RepRapLtd/WiControl/ESP-8266/UsedRepos/ESP8266 /TOP VIEW.jpg

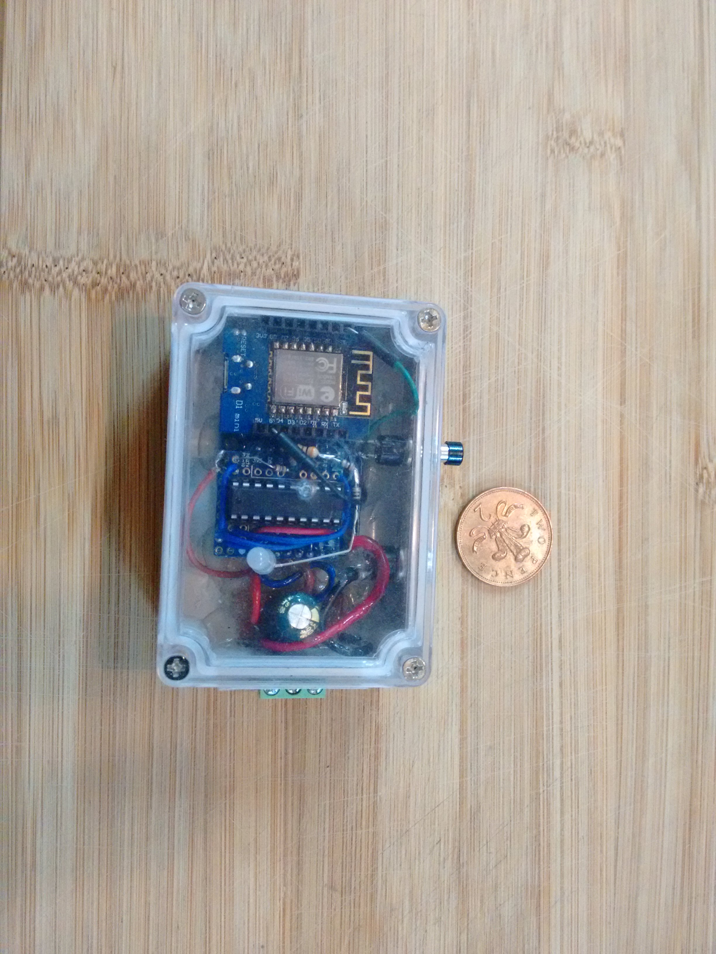
ESP-8266/UsedRepos/ESP8266 /TOP VIEW.jpg
