RepRapLtd/WiControl/ESP-8266/Electronics/KiCAD/SB - wifiboard-v2.png

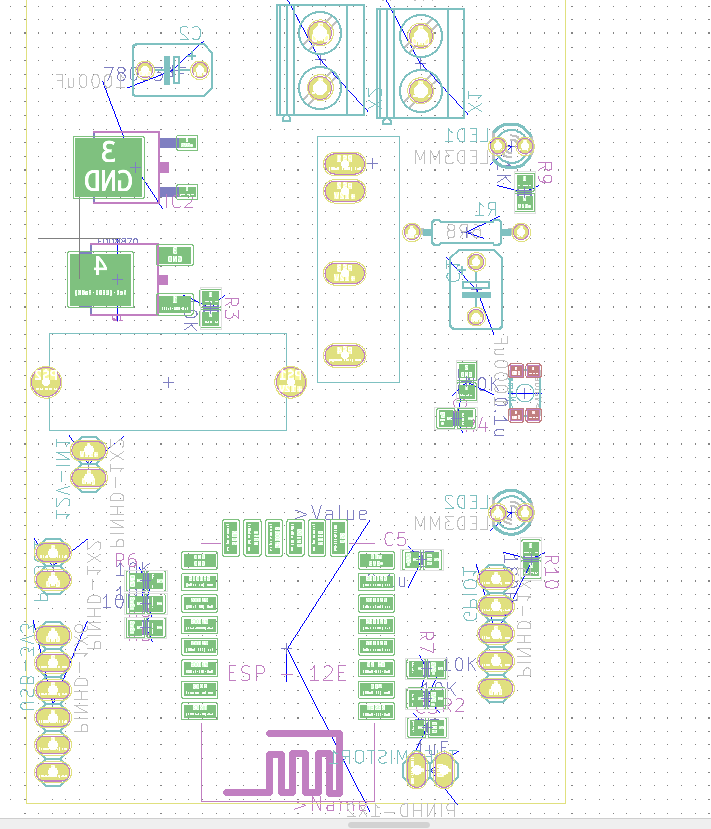
ESP-8266/Electronics/KiCAD/SB - wifiboard-v2.png
