RepRapLtd/WiControl/ESP-8266/UsedRepos/ESP8266 /OUTPUTS.jpg

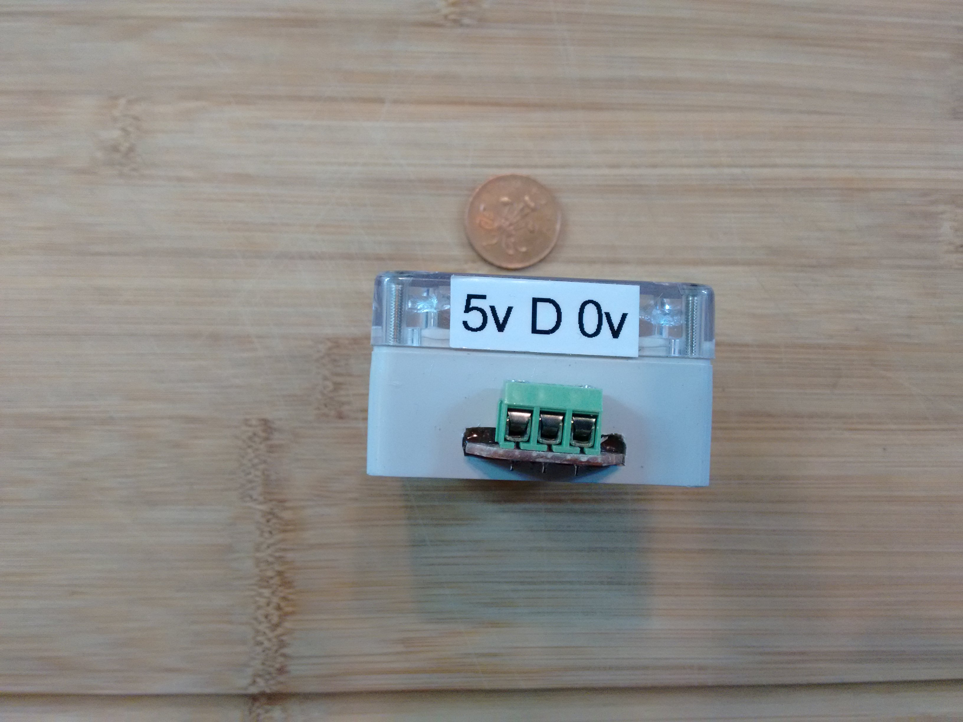
ESP-8266/UsedRepos/ESP8266 /OUTPUTS.jpg
