RepRapLtd/WiControl/ESP-8266/UsedRepos/ESP8266 /RESET BUTTON AND PSU PLUG.jpg

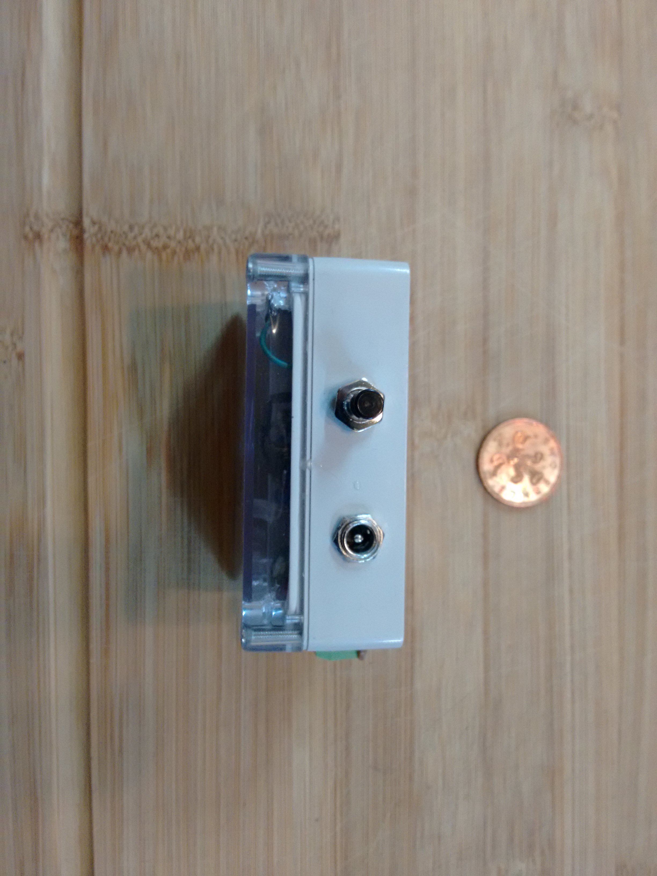
ESP-8266/UsedRepos/ESP8266 /RESET BUTTON AND PSU PLUG.jpg
