RepRapLtd/WiControl/ESP-8266/UsedRepos/ESP8266 /Wemos D1 ws2812b.jpg

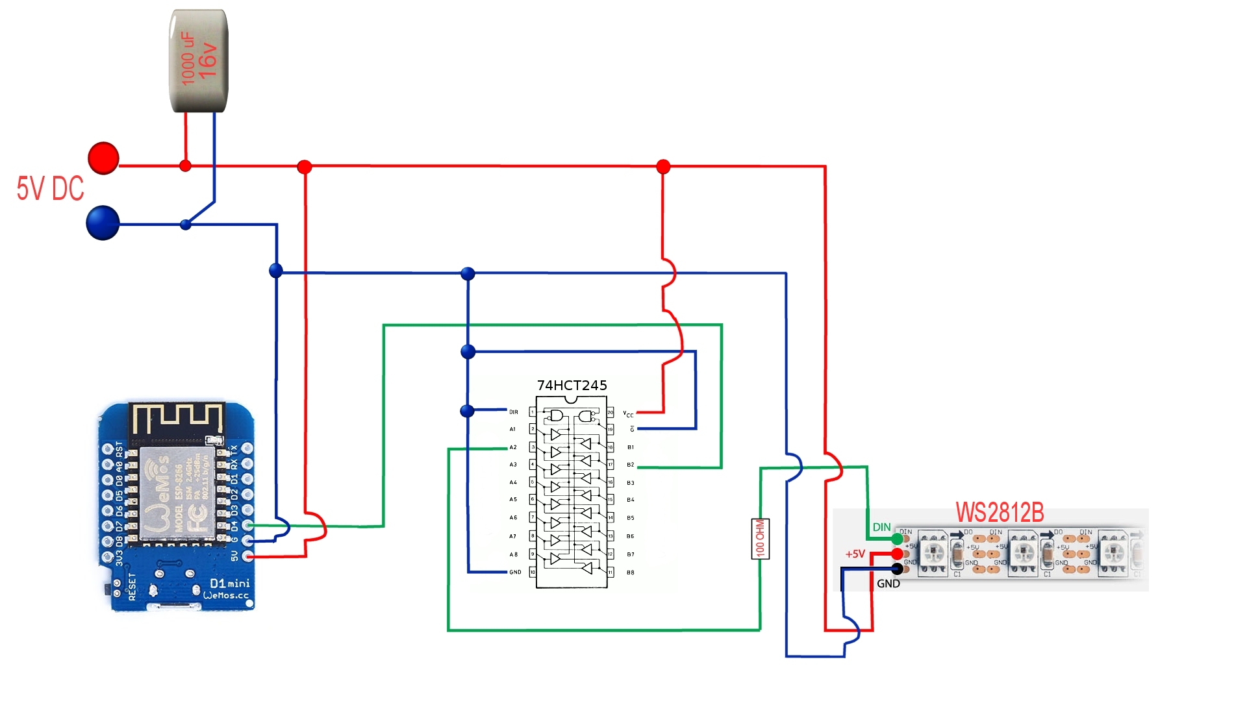
ESP-8266/UsedRepos/ESP8266 /Wemos D1 ws2812b.jpg
