RepRapLtd/WiControl/Reprogrammed-switches/swa1.jpg

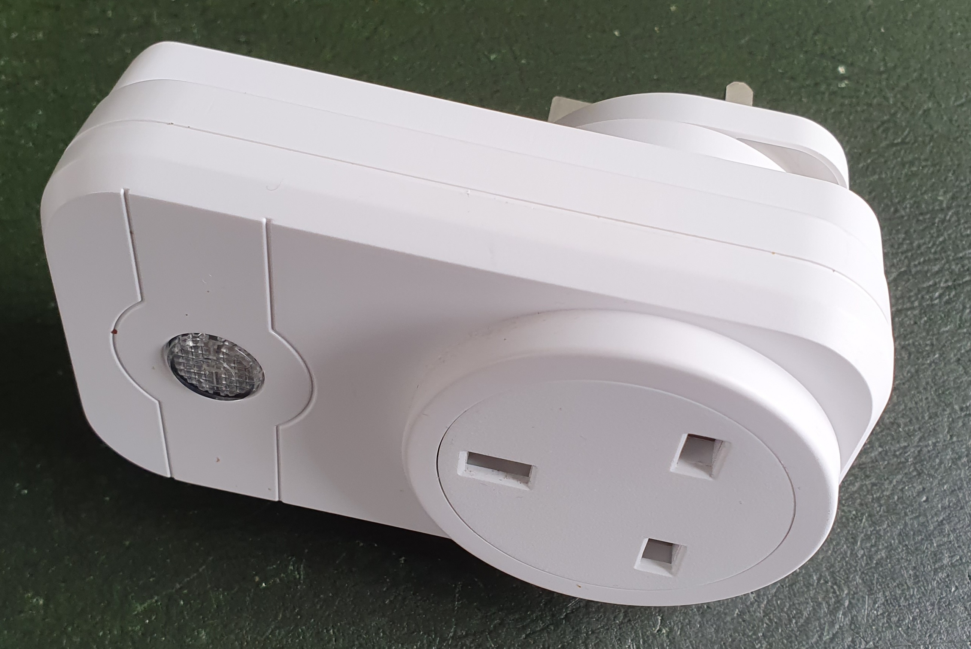
Reprogrammed-switches/swa1.jpg
