RepRapLtd/WiControl/ESP-8266/Mechanics/STLs/Wifi Patress Box/Wifi Patress-Cut014.stl

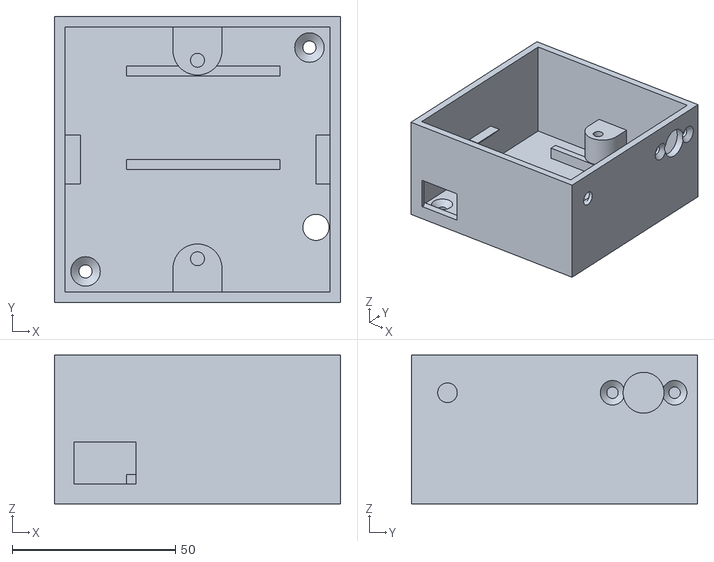
[picture p23: CAD file, 2021-06-18]
ESP-8266/Mechanics/STLs/Wifi Patress Box/Wifi Patress-Cut014.stl
87.5 x 87.5 x 45.5
