RepRapLtd/WiControl/PanStamp/Mechanical/long-lid.stl

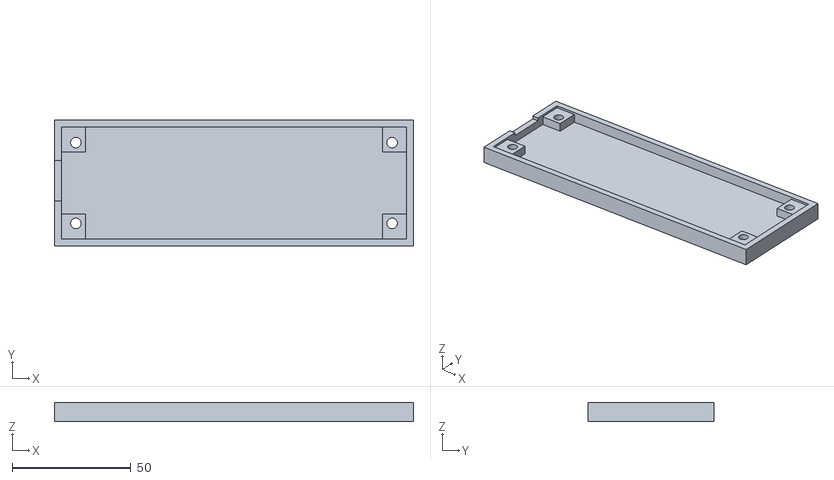
[picture p24: CAD file, 2014-07-27]
PanStamp/Mechanical/long-lid.stl
151.0 x 53.0 x 8.00
