RepRapLtd/WiControl/ESP-8266/Mechanics/Disc-STLs/walls.stl

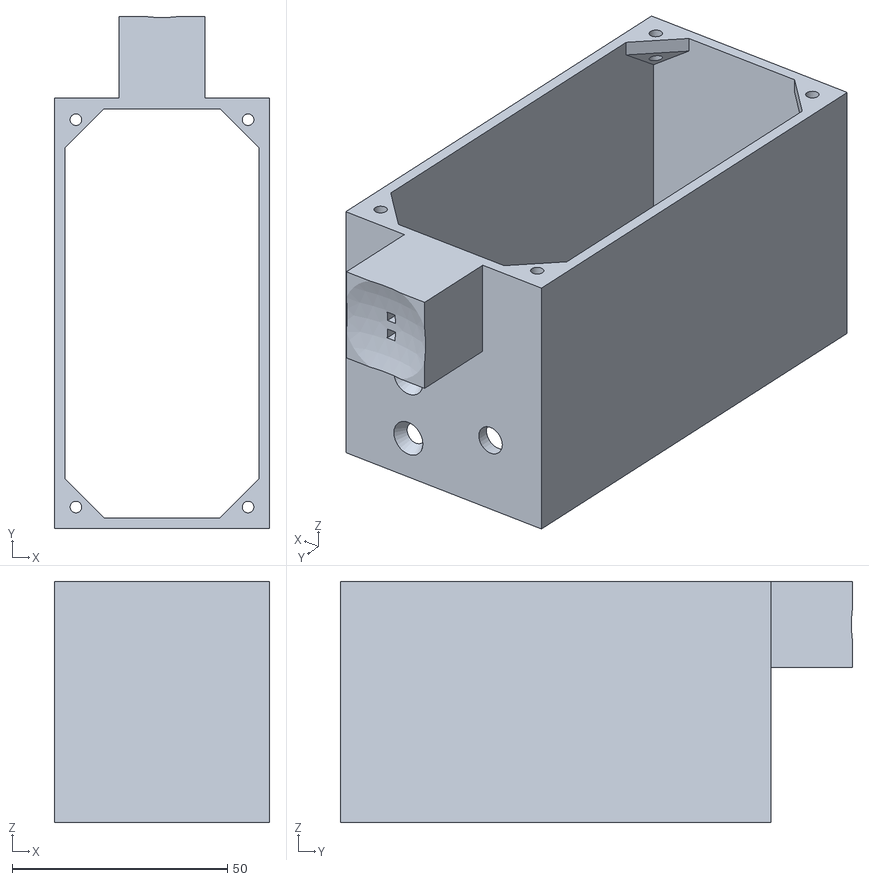
[picture p25: CAD file, 2018-09-07]
ESP-8266/Mechanics/Disc-STLs/walls.stl
50.0 x 119.0 x 56.0
