RepRapLtd/WiControl/ESP-8266/Mechanics/STLs/Bump-STLs/separator.stl

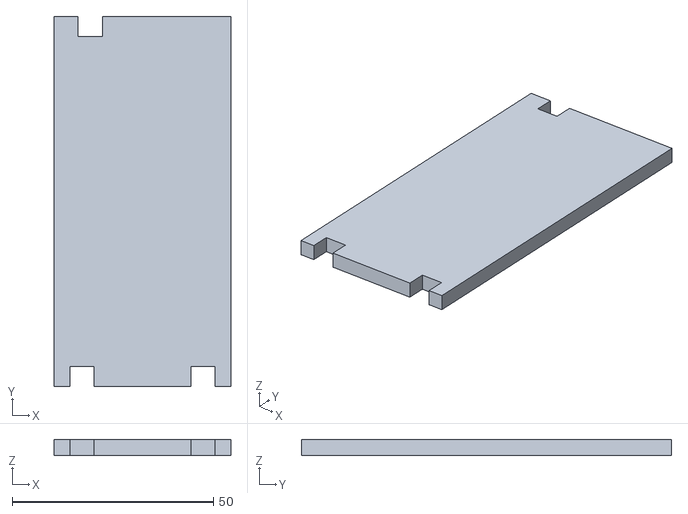
[picture p26: CAD file, 2018-09-18]
ESP-8266/Mechanics/STLs/Bump-STLs/separator.stl
44.0 x 92.0 x 4.00
