RepRapLtd/WiControl/ESP-8266/Mechanics/STLs/temp-wall-mount.stl

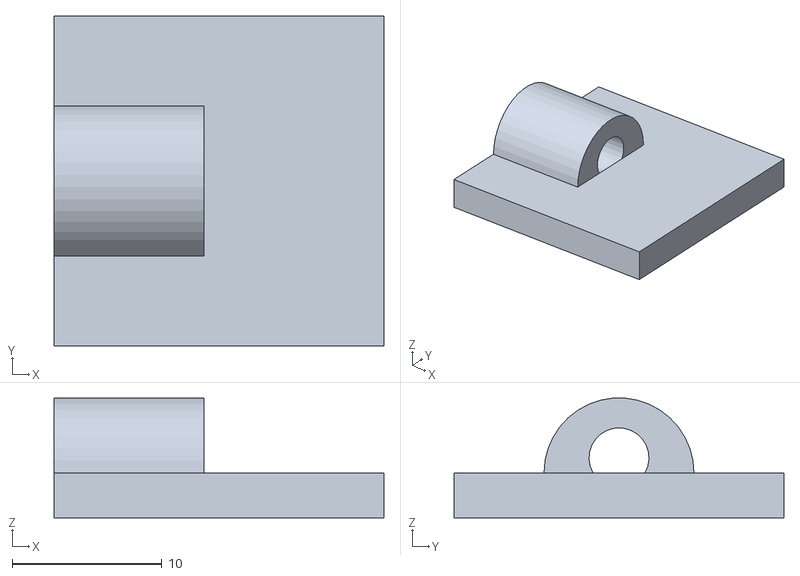
[picture p27: CAD file, 2019-10-18]
ESP-8266/Mechanics/STLs/temp-wall-mount.stl
22.0 x 22.0 x 7.98
