RepRapLtd/WiControl/PanStamp/Mechanical/long-case.stl

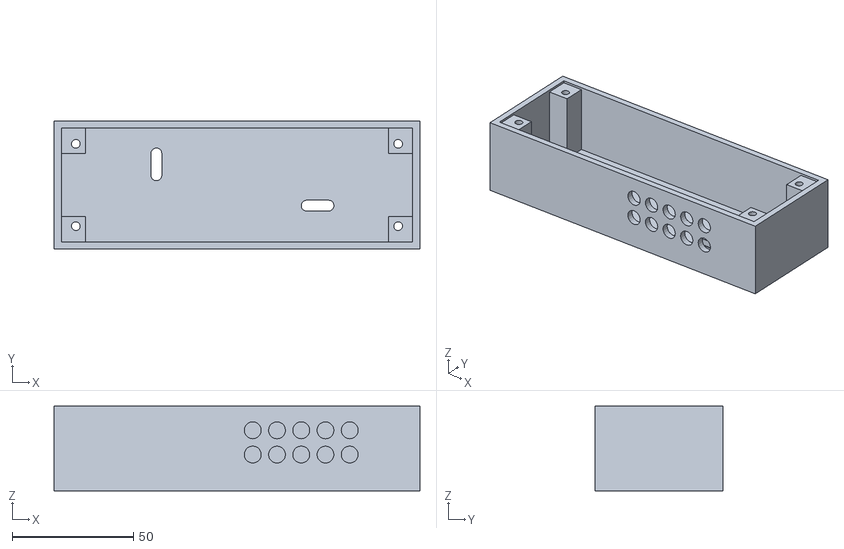
[picture p28: CAD file, 2014-07-27]
PanStamp/Mechanical/long-case.stl
151.0 x 53.0 x 35.0
