RepRapLtd/WiControl/ESP-8266/Mechanics/Disc-STLs/led-cover.stl

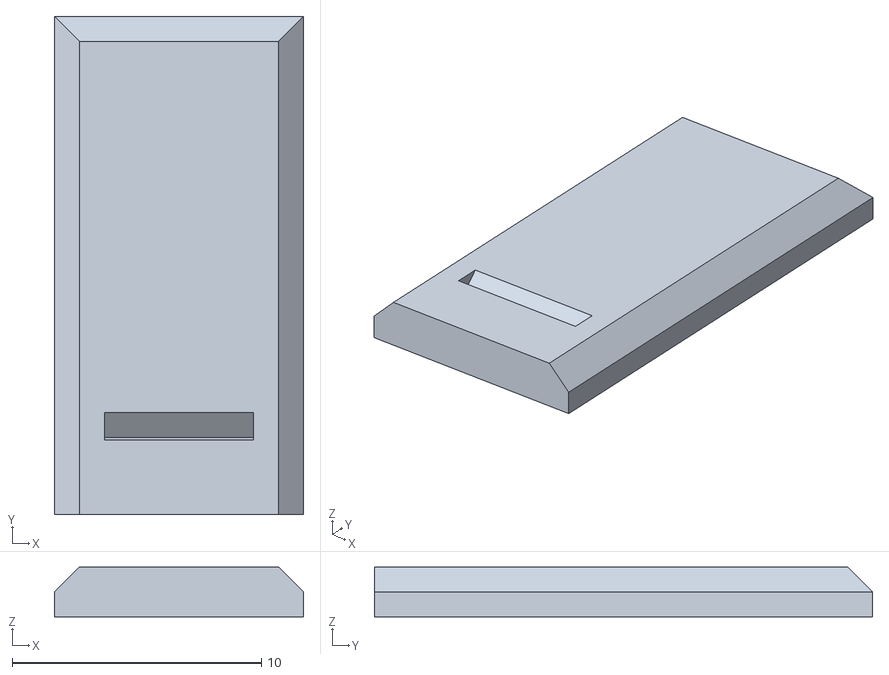
[picture p29: CAD file, 2018-09-07]
ESP-8266/Mechanics/Disc-STLs/led-cover.stl
10.0 x 20.0 x 2.00
