RepRapLtd/WiControl/ESP-8266/Mechanics/Wifi Patress.FCStd

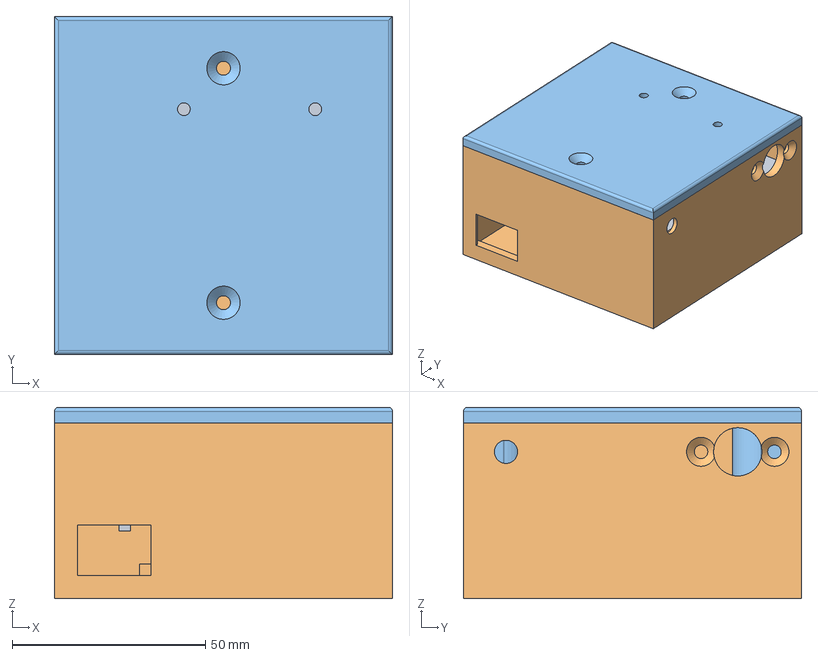
[picture p30: CAD file, 2022-01-11]
ESP-8266/Mechanics/Wifi Patress.FCStd
87.5 x 87.5 x 49.5 mm
Divider003
Lid Chamfer008
