RepRapLtd/WiControl/PanStamp/Mechanical/notch-lid.stl

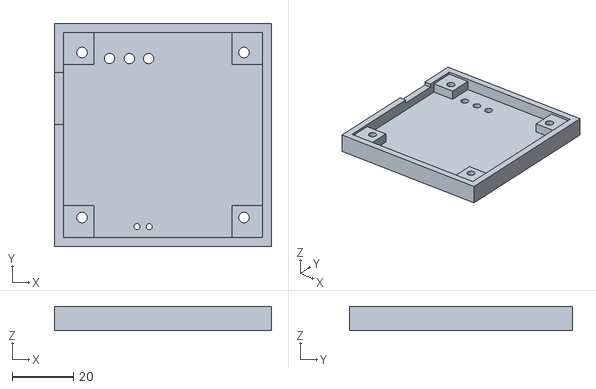
[picture p31: CAD file, 2014-07-27]
PanStamp/Mechanical/notch-lid.stl
71.0 x 73.0 x 8.00
