RepRapLtd/WiControl/ESP-8266/Mechanics/STLs/Bump-STLs/base.stl

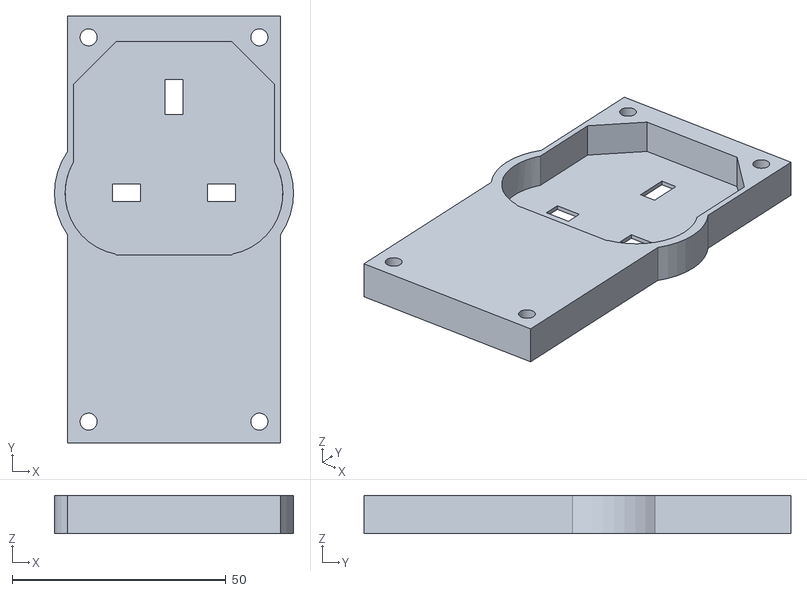
[picture p32: CAD file, 2018-09-18]
ESP-8266/Mechanics/STLs/Bump-STLs/base.stl
56.0 x 100.0 x 9.00
