RepRapLtd/WiControl/ESP-8266/Mechanics/STLs/Wifi Patress Box/Wifi Patress-Divider003.stl

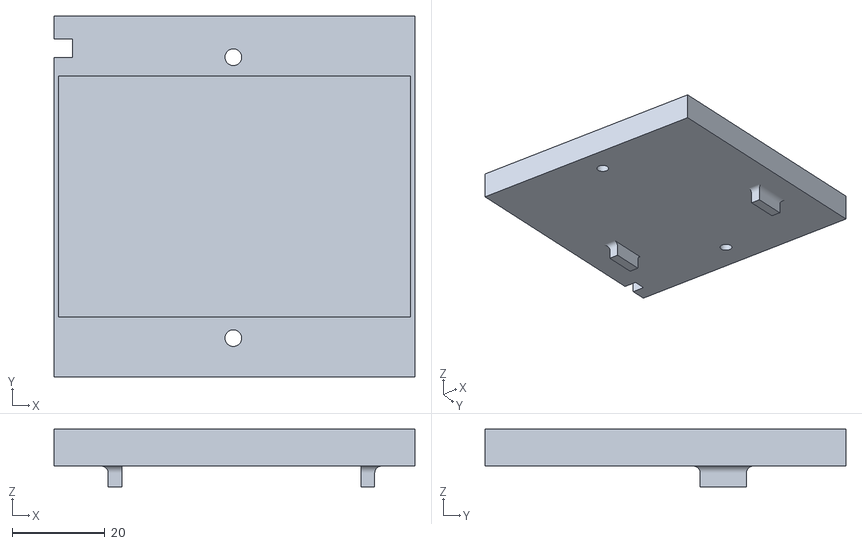
[picture p33: CAD file, 2021-06-18]
ESP-8266/Mechanics/STLs/Wifi Patress Box/Wifi Patress-Divider003.stl
78.0 x 78.0 x 12.5
