RepRapLtd/WiControl/ESP-8266/Mechanics/wifi-case-bumpy.fcstd

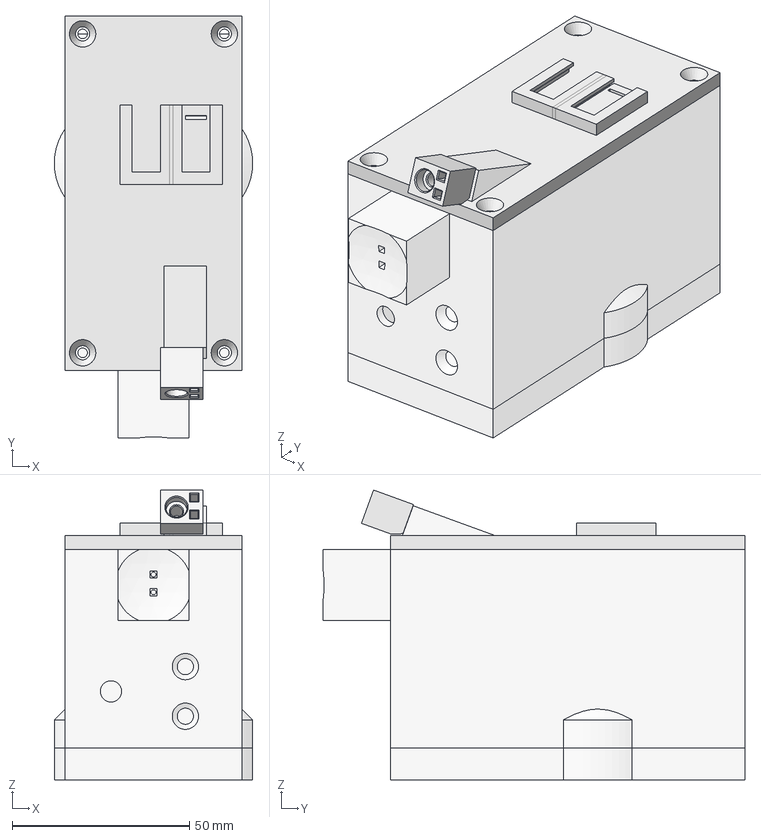
[picture p34: CAD file, 2019-11-14]
ESP-8266/Mechanics/wifi-case-bumpy.fcstd
56.0 x 119.0 x 81.9 mm
separator
LED-cover
base
lid
lid-with-connector
plug
walls
