RepRapLtd/WiControl/ESP-8266/Mechanics/Disc-STLs/cable-clamp.stl

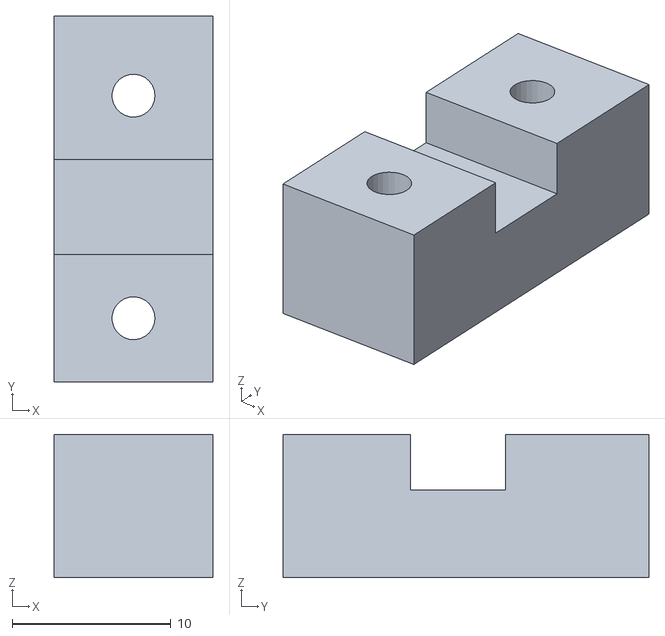
[picture p35: CAD file, 2017-12-07]
ESP-8266/Mechanics/Disc-STLs/cable-clamp.stl
10.0 x 23.0 x 9.00
