RepRapLtd/WiControl/ESP-8266/Mechanics/Temp Sensor Wall Mount.fcstd

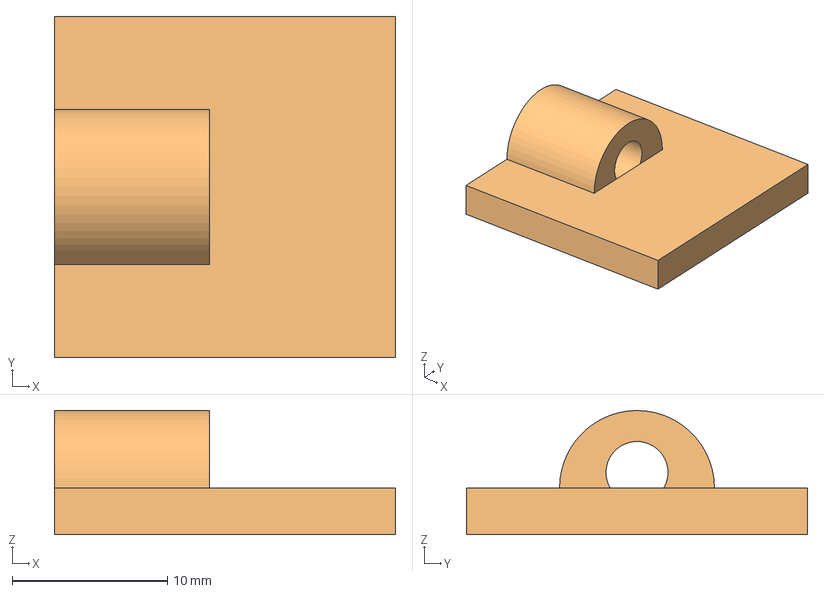
[picture p36: CAD file, 2019-07-01]
ESP-8266/Mechanics/Temp Sensor Wall Mount.fcstd
22.0 x 22.0 x 8.00 mm
Sticky Pad
