RepRapLtd/WiControl/PanStamp/Mechanical/case.stl

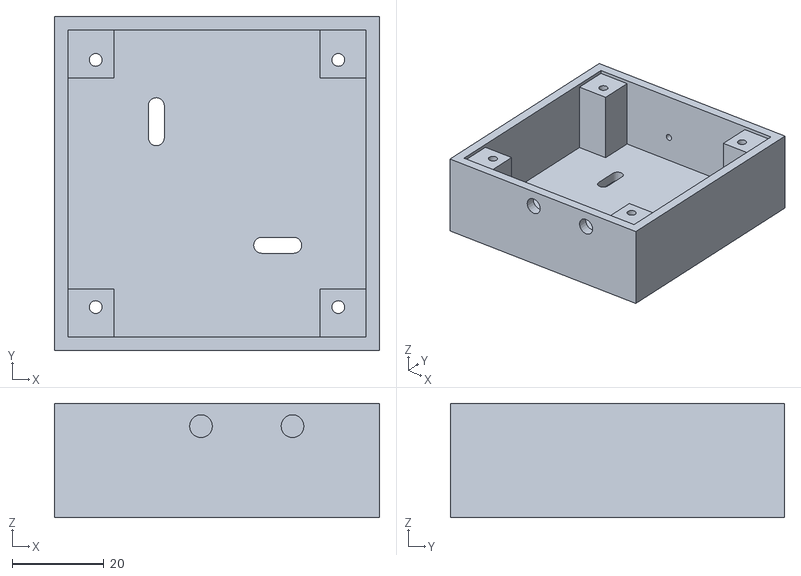
[picture p37: CAD file, 2014-01-07]
PanStamp/Mechanical/case.stl
71.0 x 73.0 x 25.0
