RepRapLtd/WiControl/ESP-8266/Mechanics/wifi-case-round.fcstd

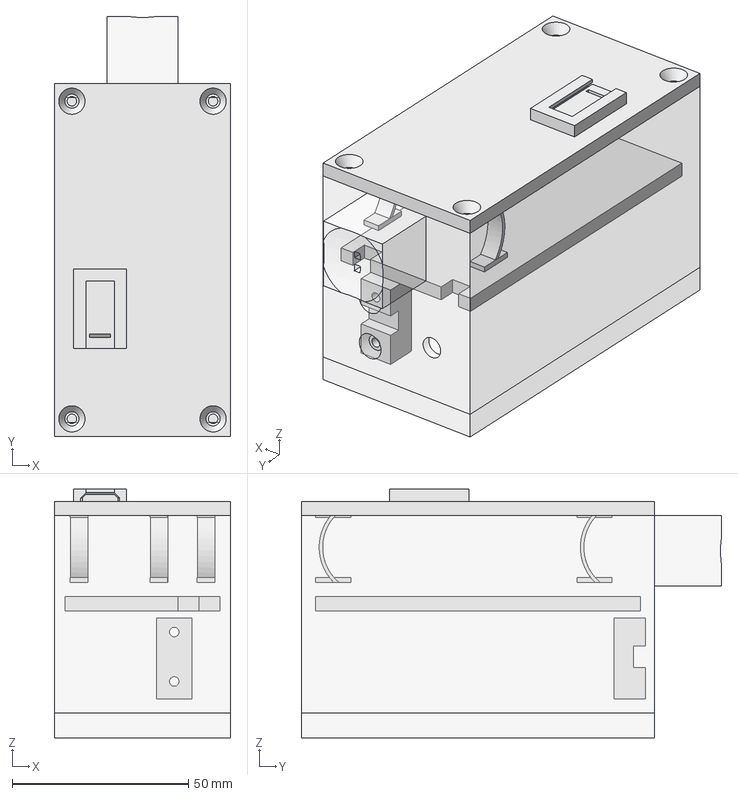
[picture p38: CAD file, 2018-09-18]
ESP-8266/Mechanics/wifi-case-round.fcstd
50.0 x 119.0 x 70.5 mm
cable-clamp
separator
base
walls
spring
spring001
spring002
LED-cover
lid
