RepRapLtd/WiControl/ESP-8266/Software/Client/OtherFunctions/Alexa-Client/Alexa-Client.ino

#include <ESPAsyncTCP.h>
#include <SyncClient.h>
#include <tcp_axtls.h>
#include <ESPAsyncTCPbuffer.h>
#include <async_config.h>
#include <AsyncPrinter.h>

#include <fauxmoESP.h>
#include <WeMo.h>

void setup() {
  // put your setup code here, to run once:

}

void loop() {
  // put your main code here, to run repeatedly:

}
