RepRapLtd/WiControl/ESP-8266/UsedRepos/ESP8266 /Alexa-kitchen-light/UpnpBroadcastResponder.h

#ifndef UPNPBROADCASTRESPONDER_H
#define UPNPBROADCASTRESPONDER_H




 
#include <Arduino.h>
#include <ESP8266WiFi.h>
#include <WiFiUdp.h>
#include "Switch.h"

class UpnpBroadcastResponder {
private:
        WiFiUDP UDP;  
public:
        UpnpBroadcastResponder();
        ~UpnpBroadcastResponder();
        bool beginUdpMulticast();
        void serverLoop();
        void addDevice(Switch *device);
};
 
#endif
