RepRapLtd/WiControl/PanStamp/Panstamp-Control/PanstampControl/Debug.ino

/*
 * Debug.cpp
 *
 *  Created on: 31 Jan 2016
 *      Author: ensab
 */

Message::Message()
{
  debug = false;
  Serial.begin(BAUD_RATE);
}

void Message::DebugOn()
{
  debug = true;
  Serial.print("Debugging on");
#ifdef WATCHDOG
  Serial.println(", watchdog active.");
#else
  Serial.println(", watchdog inactive.");
#endif
}

void Message::DebugOff()
{
  debug = false;
  Serial.println("Debugging off");
}

void Message::Debug(char* string)
{
  if(!debug)
    return;
  Serial.print(string);
}

void Message::Debug(int i)
{
  if(!debug)
    return;
  Serial.print(i);
}

void Message::Debug(float f)
{
  if(!debug)
    return;
  Serial.print(f);
}

void Message::Debug(unsigned long l)
{
  if(!debug)
    return;
  Serial.print(l);
}

void Message::Say(char* string)
{
  Serial.print(string);
}

void Message::Say(int i)
{
  Serial.print(i);
}


void Message::Say(float f)
{
  Serial.print(f);
}

void Message::Say(unsigned long l)
{
  Serial.print(l);
}
